lucaji/OpenThereminV4/OpenThereminV4/src/wavetable_0.h

/* Theremin WAVE Table - 1024 entries full table, amplitude -2048..2048*/

#include <avr/pgmspace.h>

const int16_t wavetable_0[1024] PROGMEM = {
273,
288,
302,
317,
330,
345,
358,
373,
387,
401,
416,
429,
444,
457,
472,
485,
500,
513,
527,
540,
555,
568,
581,
596,
609,
623,
636,
650,
663,
676,
690,
703,
716,
730,
743,
756,
770,
783,
796,
808,
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
};
