lucaji/OpenThereminV4/OpenThereminV4/src/wavetable_1.h

/* Theremin WAVE Table "Phoenix" - 1024 entries full table, amplitude -2048..2048*/

#include <avr/pgmspace.h>

const int16_t wavetable_1[1024] PROGMEM = {
0,
2,
3,
5,
6,
10,
11,
13,
14,
16,
19,
21,
22,
24,
26,
29,
30,
32,
33,
36,
38,
40,
41,
43,
46,
48,
49,
51,
53,
56,
58,
59,
61,
63,
67,
69,
70,
72,
74,
78,
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
};
