lucaji/OpenThereminV4/OpenThereminV4/src/wavetable_2.h

/* Theremin WAVE Table "Sinus" - 1024 entries full table, amplitude -2048.,*/

#include <avr/pgmspace.h>

const int16_t wavetable_2[1024] PROGMEM = {
9,
13,
15,
15,
18,
20,
22,
26,
30,
34,
38,
42,
46,
50,
54,
58,
62,
66,
70,
74,
78,
82,
86,
90,
92,
95,
97,
101,
105,
109,
113,
120,
124,
128,
131,
135,
135,
135,
143,
150,
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
};
