lucaji/OpenThereminV4/OpenThereminV4/src/wavetable_5.h

/* Theremin WAVE Table "Sinus" - 1024 entries full table, amplitude -2048.,*/

#include <avr/pgmspace.h>

const int16_t wavetable_5[1024] PROGMEM = {
0,
5,
10,
20,
25,
27,
33,
36,
37,
43,
46,
47,
52,
56,
59,
62,
64,
67,
71,
74,
77,
80,
82,
88,
92,
94,
98,
104,
107,
112,
115,
117,
120,
122,
126,
129,
131,
134,
138,
141,
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
};
