lucaji/OpenThereminV4/OpenThereminV4/src/wavetable_7.h

/* Theremin WAVE Table "Sinus" - 1024 entries full table, amplitude -2048.,*/

#include <avr/pgmspace.h>

const int16_t wavetable_7[1024] PROGMEM = {
11,
42,
47,
51,
56,
69,
80,
91,
102,
112,
123,
130,
138,
145,
152,
159,
166,
174,
181,
188,
195,
202,
210,
217,
224,
231,
238,
246,
253,
260,
267,
274,
282,
289,
297,
304,
312,
327,
334,
342,
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
};
